okayumoka/Natsumi/pictures/picture_03.jpg

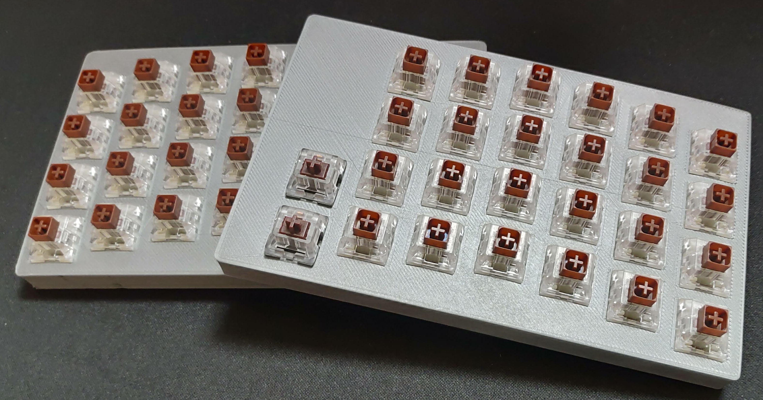
pictures/picture_03.jpg
