okayumoka/Natsumi/pictures/picture_05.jpg

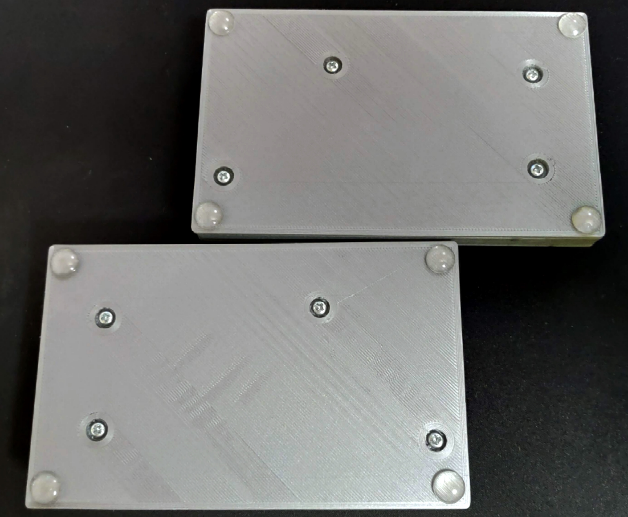
pictures/picture_05.jpg
