okayumoka/Natsumi/pictures_work/picture_01.jpg

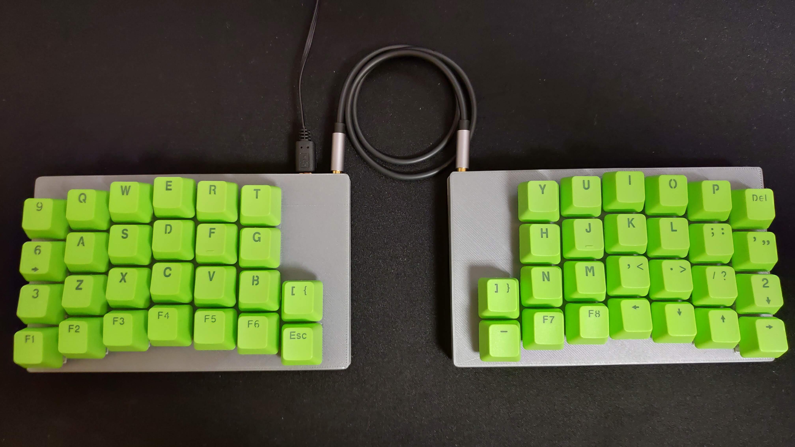
pictures_work/picture_01.jpg
