okayumoka/Natsumi/pictures_work/picture_02.jpg

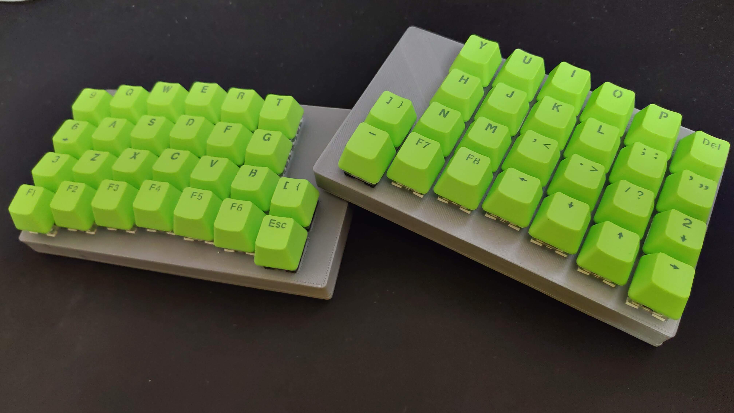
pictures_work/picture_02.jpg
