okayumoka/Natsumi/pictures_work/picture_03.jpg

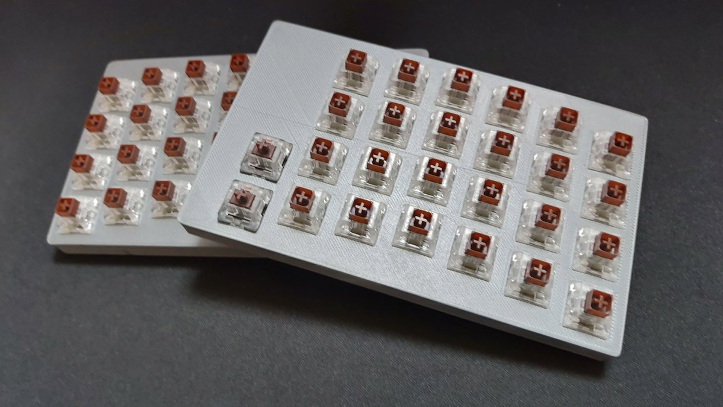
pictures_work/picture_03.jpg
