okayumoka/Natsumi/pictures_work/picture_04.jpg

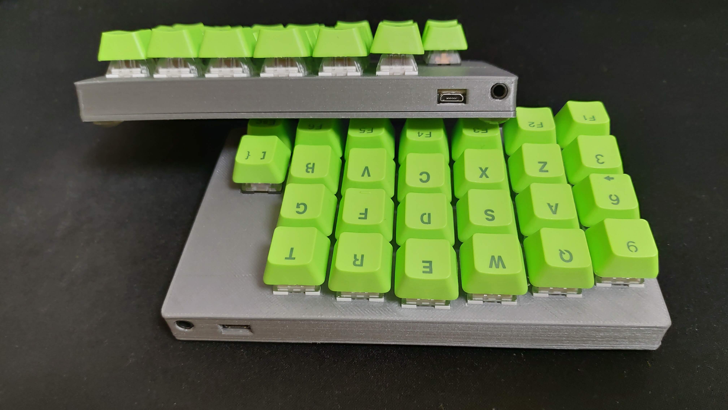
pictures_work/picture_04.jpg
