okayumoka/Natsumi/pictures_work/picture_05.jpg

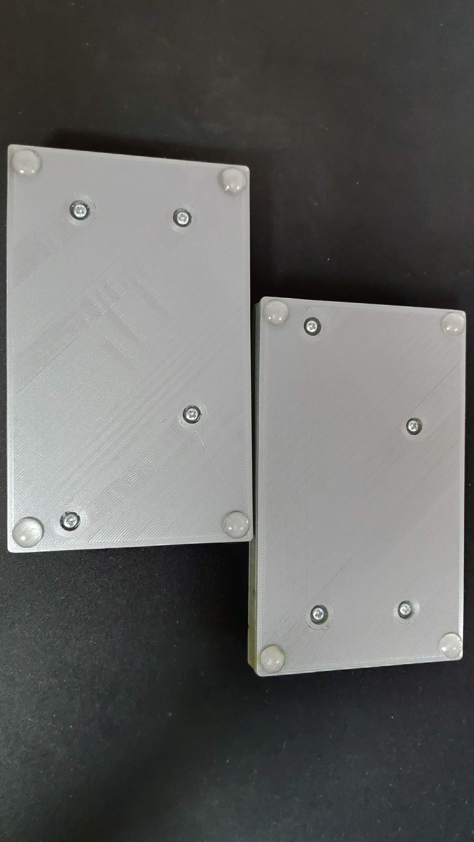
pictures_work/picture_05.jpg
