okayumoka/Natsumi/pictures_work/picture_06.jpg

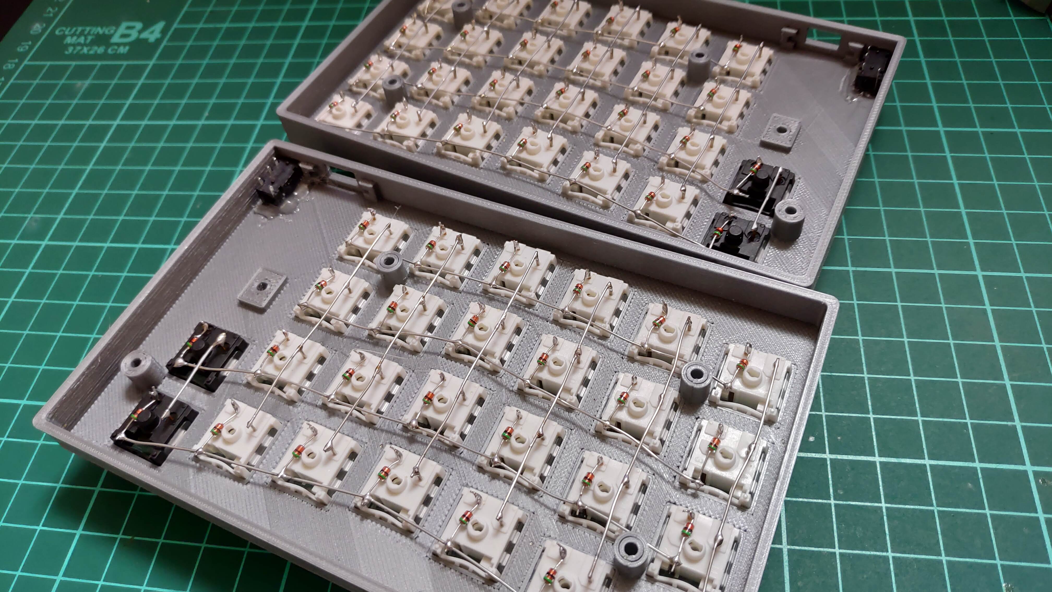
pictures_work/picture_06.jpg
