okayumoka/Natsumi/pictures_work/picture_08.jpg

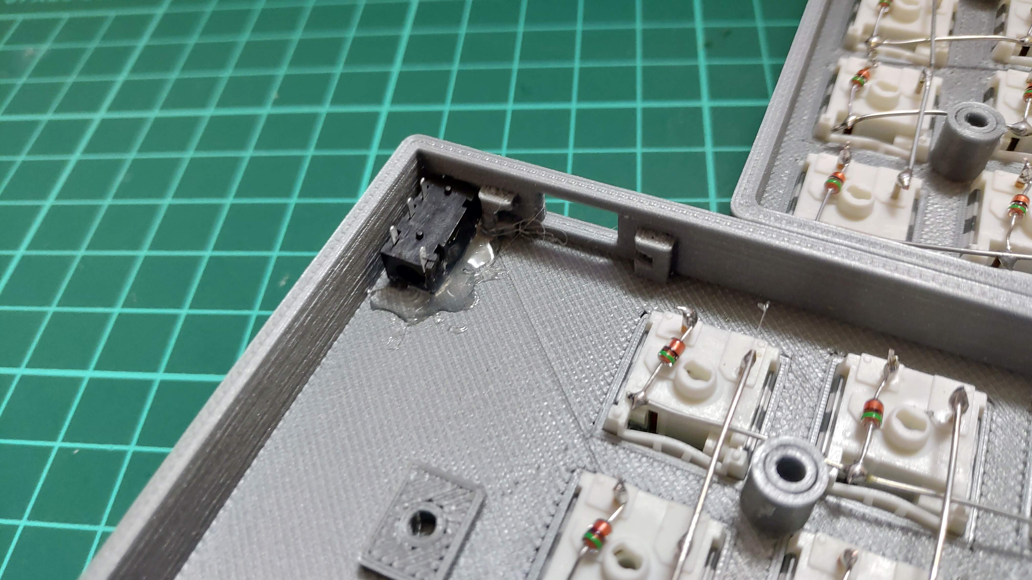
pictures_work/picture_08.jpg
