okayumoka/Natsumi/pictures_work/picture_09.jpg

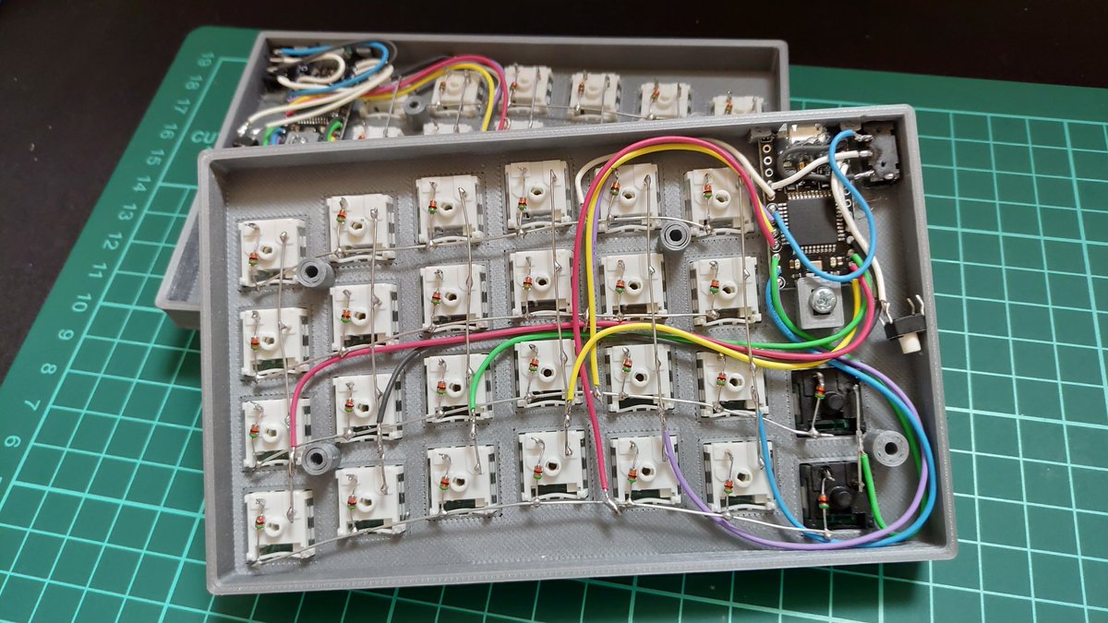
pictures_work/picture_09.jpg
