okayumoka/Natsumi/wiring/wiring_diagram.png

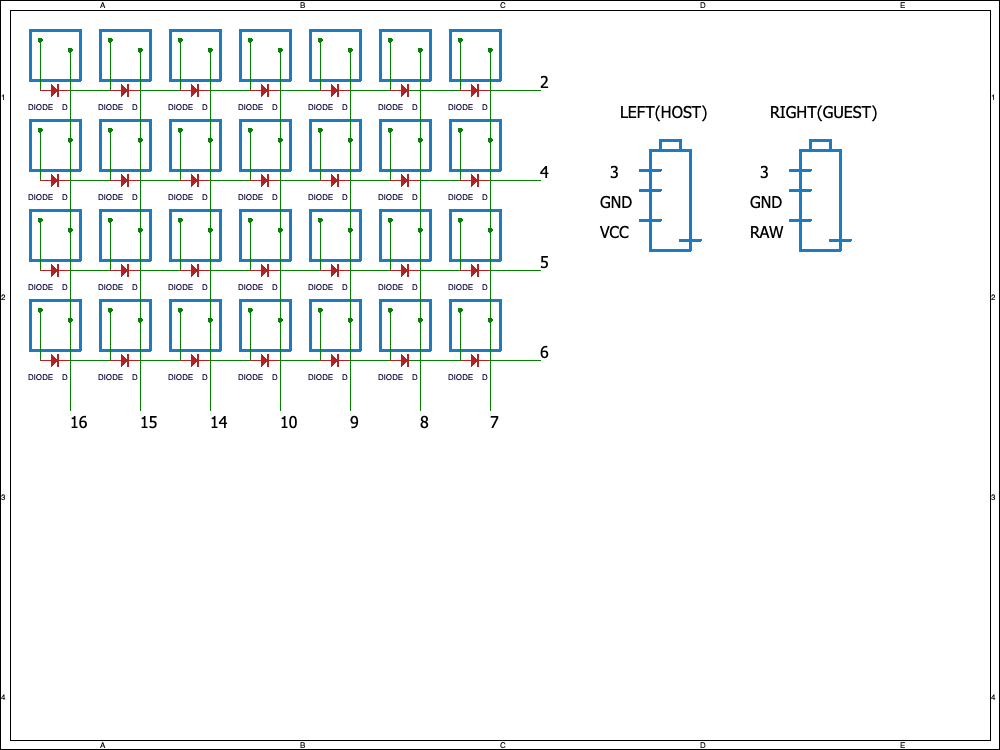
wiring/wiring_diagram.png
